wilhelmzeuschner/bachelor_thesis_wilhelm/code/lmm_firmware/doc/html/main_8cpp_a4fc01d736fe50cf5b977f755b675f11d_cgraph.png

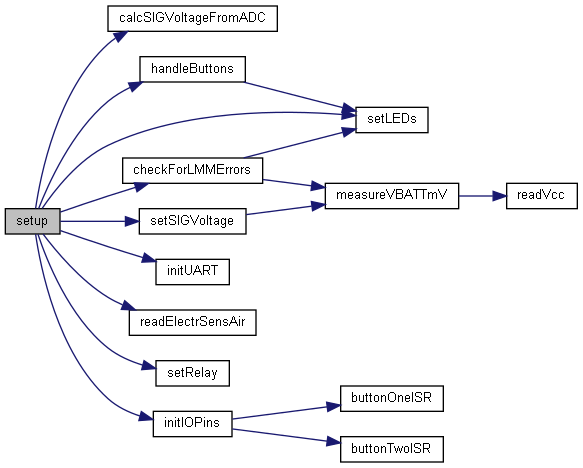
code/lmm_firmware/doc/html/main_8cpp_a4fc01d736fe50cf5b977f755b675f11d_cgraph.png
